acestronautical/RoofFlangeForge/cli/scad/trapezoidal_roof.scad

// =============================================================================
// trapezoidal_roof.scad
//
// Parametric model of a periodic sheet-metal roof whose cross-section is a
// series of flat rib plateaus separated by trapezoidal indent valleys. Every
// dimension is a top-level variable and can be overridden with OpenSCAD's -D
// flag, so this file can drive adapter designs for any roof with the same
// profile family.
//
// Exports:
//     module trapezoidal_roof_cutter(...)   - solid block on one side of the
//                                             roof surface, sized for
//                                             subtraction from a ring blank.
//     module trapezoidal_roof_sheet(...)    - thin sheet-metal-like
//                                             visualization of the roof.
//
// All dimensions are in inches; unit conversion happens in the consumer.
// =============================================================================

// -----------------------------------------------------------------------------
// Roof cross-section defaults (inches). Every one is overridable via -D.
// -----------------------------------------------------------------------------
rib_width      = 3.500;        // rib plateau width (flat top between indents)
indent_top_w   = 2.000;        // indent width at rib plateau level (top of the trapezoid)
indent_bot_w   = 1.500;        // indent width at the floor              (bottom of the trapezoid)
indent_depth   = 0.500;        // vertical drop from rib plateau to indent floor
corner_r       = 0.0625;       // convex bend radius on the rib-to-sidewall corners
sheet_thickness = 0.032;       // sheet-metal gauge (~0.8 mm typical automotive body panel)

// Derived
roof_pitch          = rib_width + indent_top_w;                    // rib CL to next rib CL
indent_center_x     = rib_width/2 + indent_top_w/2;                // rib CL to adjacent indent CL

// =============================================================================
// trapezoidal_roof_cutter(flange_offset_x, top_w, bot_w, depth, r,
//                         cut_xy, cut_z, side)
//
// A solid block on one side of the roof surface, sized so the roof is fully
// captured within its X-Y footprint. Subtract from a ring blank to carve the
// roof profile into it.
//
// The block's top surface (when side == "top") sits at Z = 0 at rib plateau
// level and drops into trapezoidal valleys at every indent centerline.
//
// Parameters:
//   flange_offset_x - horizontal shift of the roof pattern under the flange:
//                    0                 -> a rib centerline sits at X = 0
//                    indent_center_x   -> an indent centerline sits at X = 0
//                    any real value    -> arbitrary off-center placement
//   top_w        - indent top width to carve  (default: real roof indent_top_w)
//   bot_w        - indent bottom width to carve
//   depth        - indent depth to carve
//   r            - convex bend radius on the rib-to-sidewall corners
//   cut_xy       - half-width of the cutter in X and Y (large enough to cover
//                  the ring blank in every direction)
//   cut_z        - depth of the cutter block below the roof surface
//   side         - "top"    : block fills the space BELOW the roof surface
//                             (subtract to build a topside adapter)
//                  "bottom" : block fills the space ABOVE the roof surface
//                             (subtract to build an underside adapter)
// =============================================================================
module trapezoidal_roof_cutter(
    flange_offset_x = 0,
    top_w        = indent_top_w,
    bot_w        = indent_bot_w,
    depth        = indent_depth,
    r            = corner_r,
    cut_xy       = 40,
    cut_z        = 5,
    side         = "top",
    thickness    = sheet_thickness,
    tolerance    = 0
) {
    // The bottom cutter aligns with the roof's BOTTOM face (offset down from
    // the top face by the sheet-metal gauge), so top+bottom cutters leave a
    // sheet-thickness gap between them where the physical roof lives.
    z_shift = (side == "bottom") ? -thickness : 0;
    // top_y is the tiny above-plateau overlap baked into the profile; used
    // here as the plateau reference line for the tolerance clip.
    top_y = 0.010;
    translate([0, 0, z_shift])
        rotate([90, 0, 0])
            linear_extrude(height = 2*cut_xy, center = true)
                if (tolerance <= 0) {
                    trapezoidal_roof_profile_2d(
                        flange_offset_x = flange_offset_x,
                        top_w        = top_w,
                        bot_w        = bot_w,
                        depth        = depth,
                        corner_r     = r,
                        cut_xy       = cut_xy,
                        cut_z        = cut_z,
                        side         = side
                    );
                } else if (side == "top") {
                    // Cutter interior is BELOW the surface; offset pushes it
                    // upward, so clip anything that ends up above the plateau
                    // line to preserve the plateau contact face.
                    intersection() {
                        offset(delta = tolerance)
                            trapezoidal_roof_profile_2d(
                                flange_offset_x = flange_offset_x,
                                top_w        = top_w,
                                bot_w        = bot_w,
                                depth        = depth,
                                corner_r     = r,
                                cut_xy       = cut_xy,
                                cut_z        = cut_z,
                                side         = "top"
                            );
                        translate([-2*cut_xy, -2*cut_z])
                            square([4*cut_xy, 2*cut_z + top_y]);
                    }
                } else {
                    // Cutter interior is ABOVE the surface; offset pushes the
                    // surface downward. A symmetric clip at y=top_y would wipe
                    // out the indent pockets (which live below the plateau
                    // line at indent-x). Instead, union two pieces:
                    //   (1) offset polygon clipped to y >= top_y (preserves
                    //       plateau, drops the tolerance-strip that would
                    //       cut into the block's plateau face), and
                    //   (2) offset applied ONLY to the parts of the original
                    //       polygon that dipped below the plateau (the indent
                    //       bulges) so pockets get deeper by tolerance and
                    //       walls widen by tolerance per side.
                    union() {
                        intersection() {
                            offset(delta = tolerance)
                                trapezoidal_roof_profile_2d(
                                    flange_offset_x = flange_offset_x,
                                    top_w        = top_w,
                                    bot_w        = bot_w,
                                    depth        = depth,
                                    corner_r     = r,
                                    cut_xy       = cut_xy,
                                    cut_z        = cut_z,
                                    side         = "bottom"
                                );
                            translate([-2*cut_xy, top_y])
                                square([4*cut_xy, 4*cut_z]);
                        }
                        offset(delta = tolerance) intersection() {
                            trapezoidal_roof_profile_2d(
                                flange_offset_x = flange_offset_x,
                                top_w        = top_w,
                                bot_w        = bot_w,
                                depth        = depth,
                                corner_r     = r,
                                cut_xy       = cut_xy,
                                cut_z        = cut_z,
                                side         = "bottom"
                            );
                            translate([-2*cut_xy, -2*cut_z])
                                square([4*cut_xy, 2*cut_z + top_y]);
                        }
                    }
                }
}

// The 2D cross-section of the cutter. Interior of the polygon = block material.
// The rib-to-sidewall bends are chamfered directly in the surface point list
// (see trapezoidal_roof_surface_pts), so the polygon here is already smooth.
module trapezoidal_roof_profile_2d(
    flange_offset_x,
    top_w,
    bot_w,
    depth,
    corner_r,
    cut_xy,
    cut_z,
    side = "top"
) {
    top_y = 0.010;             // small overlap into positive Z (a hair above the rib plateau)

    surface_ltr = trapezoidal_roof_surface_pts(
        flange_offset_x = flange_offset_x,
        top_w        = top_w,
        bot_w        = bot_w,
        depth        = depth,
        cut_xy       = cut_xy,
        top_y        = top_y,
        r            = corner_r
    );
    n = len(surface_ltr);

    pts = (side == "top")
        ? concat(
            [[-cut_xy, -cut_z], [+cut_xy, -cut_z]],
            [ for (i = [n-1 : -1 : 0]) surface_ltr[i] ]
        )
        : concat(
            [[+cut_xy, +cut_z], [-cut_xy, +cut_z]],
            surface_ltr
        );

    polygon(pts);
}

// List of (X, Y) points that trace the roof's TOP surface across [-cut_xy, +cut_xy],
// left to right, including the trapezoidal dip into every indent in range.
// Y in the 2D plane will become Z after the caller's rotate([90,0,0]).
// When r > 0, each rib bend is replaced by two chamfer points offset by r
// along the two adjacent edges -- a straight-line chamfer of the corner.
function trapezoidal_roof_surface_pts(flange_offset_x, top_w, bot_w, depth, cut_xy, top_y, r = 0) =
    let (
        n_max     = ceil(cut_xy / roof_pitch) + 1,
        indent_xs = [
            for (k = [-n_max : n_max])
                let (ix = indent_center_x + k * roof_pitch - flange_offset_x)
                if (ix - top_w/2 >= -cut_xy && ix + top_w/2 <= cut_xy) ix
        ],
        sharp = concat(
            [[-cut_xy, top_y]],
            [ for (ix = indent_xs)
                each [
                    [ix - top_w/2, top_y],
                    [ix - bot_w/2, -depth],
                    [ix + bot_w/2, -depth],
                    [ix + top_w/2, top_y]
                ]
            ],
            [[+cut_xy, top_y]]
        )
    )
    r > 0 ? chamfer_polyline(sharp, r) : sharp;

// Replace each interior corner in a polyline with two chamfer points offset
// by r along the two adjacent edges (clamped so the chamfer can't consume
// more than 45% of either edge).
function chamfer_polyline(pts, r) =
    let (n = len(pts))
    n < 3 ? pts : concat(
        [pts[0]],
        [ for (i = [1 : n-2]) each chamfer_corner(pts[i-1], pts[i], pts[i+1], r) ],
        [pts[n-1]]
    );

function chamfer_corner(a, b, c, r) =
    let (
        v_in  = a - b,
        v_out = c - b,
        d_in  = norm(v_in),
        d_out = norm(v_out),
        r_eff = min(r, d_in * 0.45, d_out * 0.45)
    )
    [
        b + r_eff * v_in  / d_in,
        b + r_eff * v_out / d_out
    ];

// =============================================================================
// trapezoidal_roof_sheet(...)
//
// Thin sheet-metal visualization of the roof. Same top surface as
// trapezoidal_roof_cutter, but the polygon closes to a bottom that is the
// top surface offset down by `sheet_thickness`. Not used by circular_adapter;
// intended for previewing the roof shape as a stamped panel.
//
// Corners are intentionally left sharp -- applying the same offset(r=-r)
// rounding used by the cutter would erode a real body-panel-gauge sheet
// (~0.032") to nothing.
// =============================================================================
module trapezoidal_roof_sheet(
    flange_offset_x    = 0,
    top_w           = indent_top_w,
    bot_w           = indent_bot_w,
    depth           = indent_depth,
    cut_xy          = 12,
    sheet_thickness = 0.100      // visualization thickness; not physically accurate
) {
    rotate([90, 0, 0])
        linear_extrude(height = 2*cut_xy, center = true)
            trapezoidal_roof_sheet_2d(
                flange_offset_x    = flange_offset_x,
                top_w           = top_w,
                bot_w           = bot_w,
                depth           = depth,
                cut_xy          = cut_xy,
                sheet_thickness = sheet_thickness
            );
}

module trapezoidal_roof_sheet_2d(flange_offset_x, top_w, bot_w, depth, cut_xy, sheet_thickness) {
    top_y = 0.010;

    surface_ltr = trapezoidal_roof_surface_pts(
        flange_offset_x = flange_offset_x,
        top_w        = top_w,
        bot_w        = bot_w,
        depth        = depth,
        cut_xy       = cut_xy,
        top_y        = top_y,
        r            = corner_r
    );
    n = len(surface_ltr);

    // CCW: top surface RTL (interior below the top edge) then bottom surface
    // LTR (interior above the bottom edge). Interior = sheet material.
    surface_rtl = [ for (i = [n-1 : -1 : 0]) surface_ltr[i] ];
    bottom_ltr  = [ for (p = surface_ltr) [p[0], p[1] - sheet_thickness] ];

    polygon(concat(surface_rtl, bottom_ltr));
}
